Resinchem/ESP-Parking-Assistant/docs/images/mqtttopics_sample_output.jpg

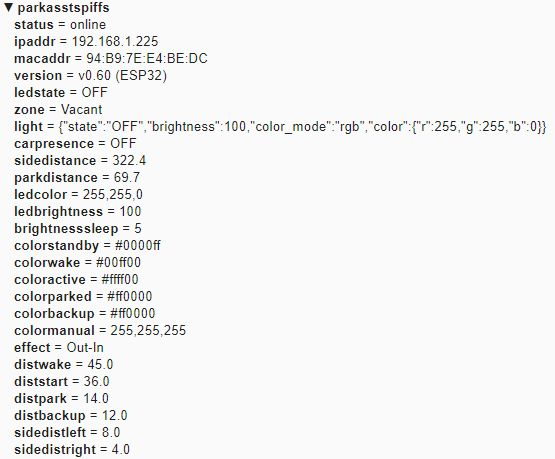
docs/images/mqtttopics_sample_output.jpg
